psycofdj/burger-quiz-v2/bquiz/resources/addition-back-arrow.png

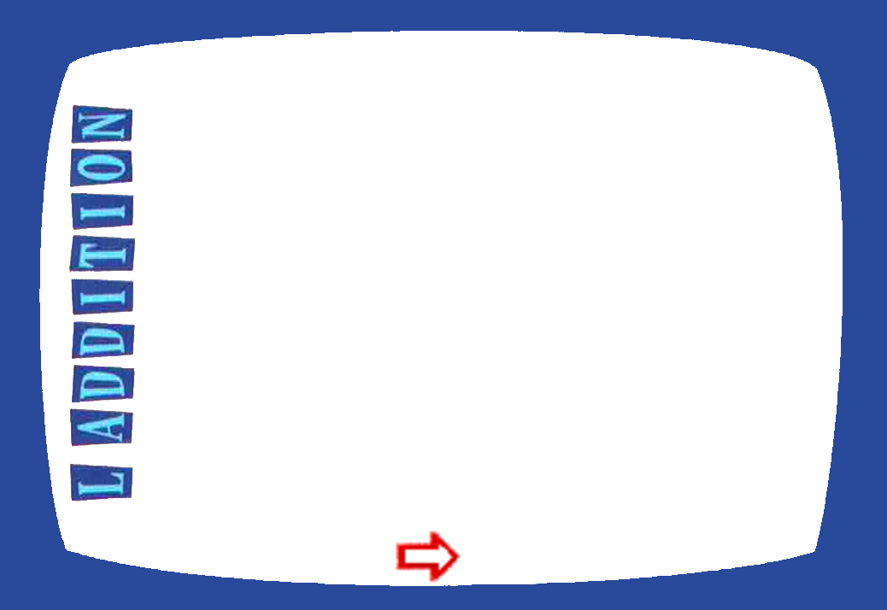
bquiz/resources/addition-back-arrow.png
