psycofdj/burger-quiz-v2/bquiz/resources/menus-back.png

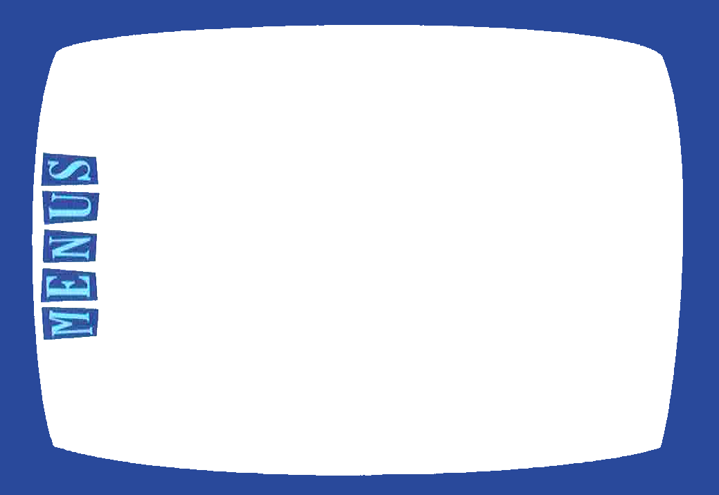
bquiz/resources/menus-back.png
